acojon/ScreamBooth/Photos/2018-08-08 17.52.51.jpg

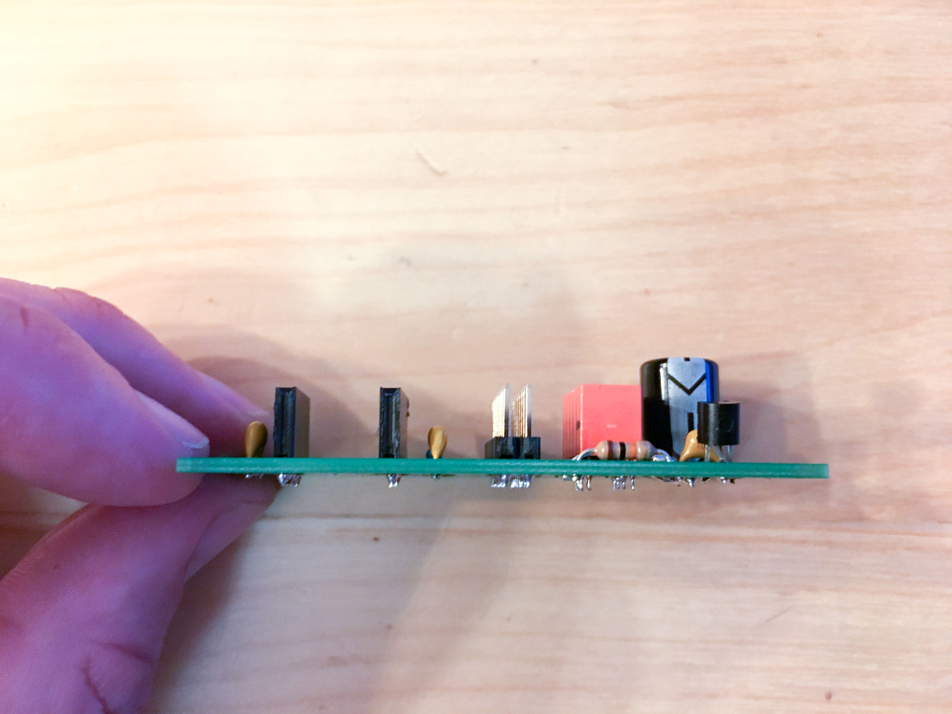
Photos/2018-08-08 17.52.51.jpg
