acojon/ScreamBooth/Photos/2018-08-08 18.09.00.jpg

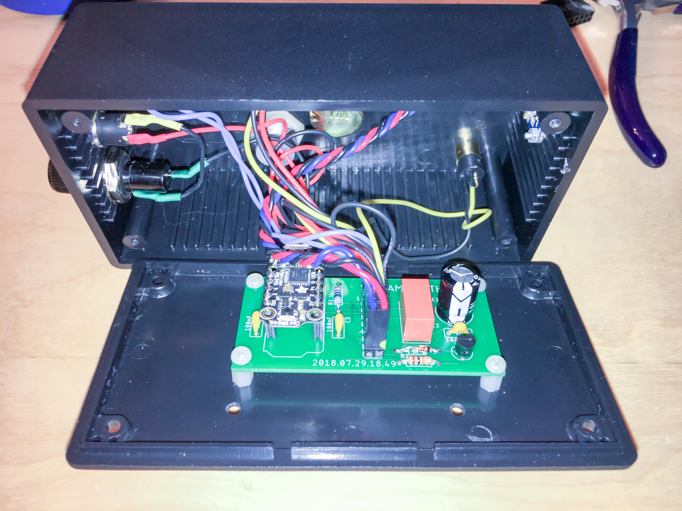
Photos/2018-08-08 18.09.00.jpg
